theqbz/KicsiKocsi/rajzok/cover.jpg

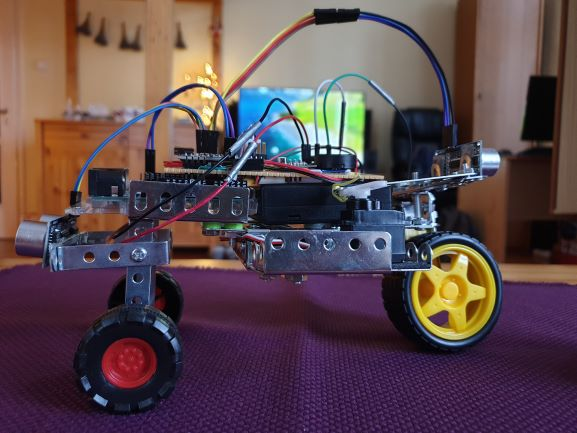
rajzok/cover.jpg
