theqbz/KicsiKocsi/rajzok/kicsikocsi1.jpg

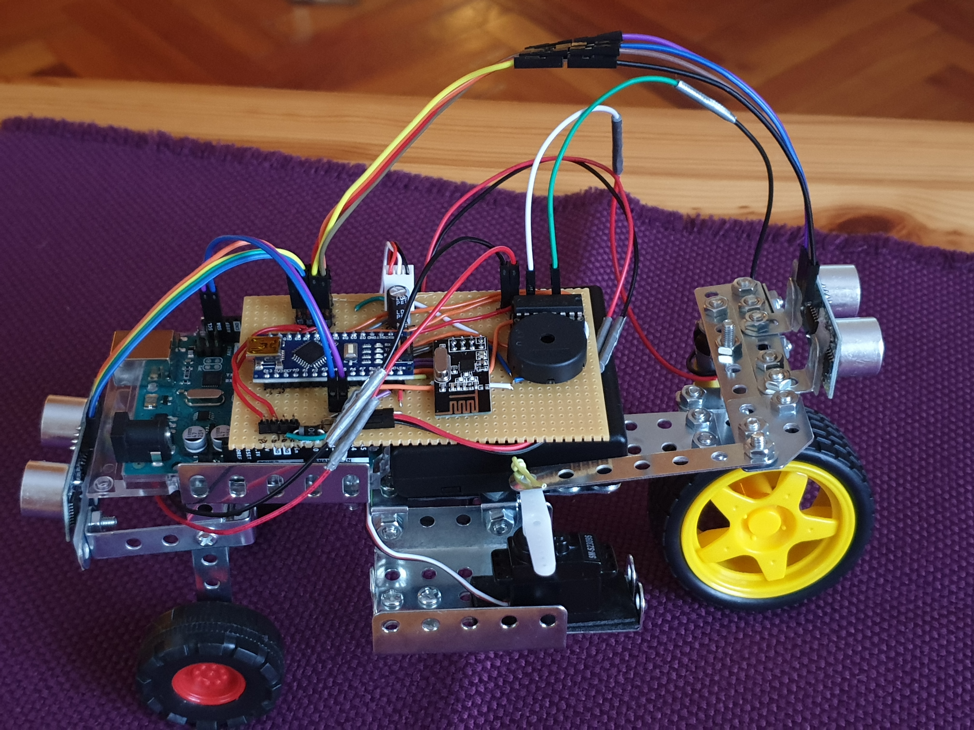
rajzok/kicsikocsi1.jpg
