theqbz/KicsiKocsi/rajzok/kicsikocsi3.jpg

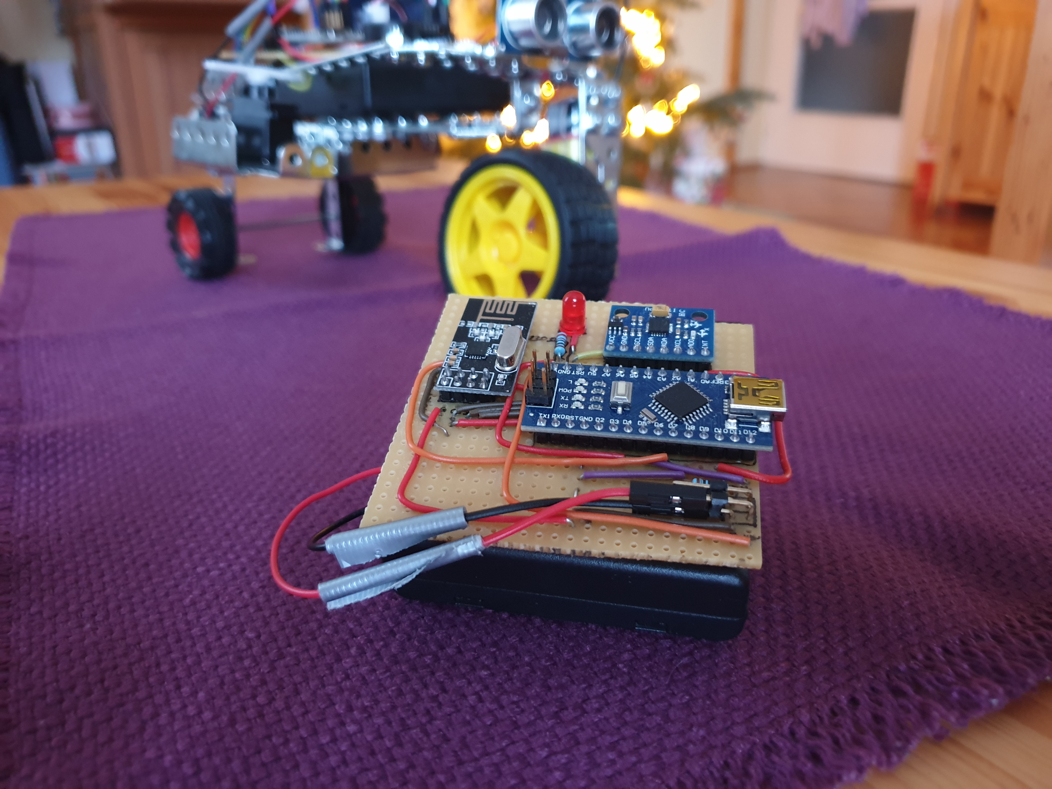
rajzok/kicsikocsi3.jpg
