theqbz/KicsiKocsi/rajzok/kicsikocsi4.jpg

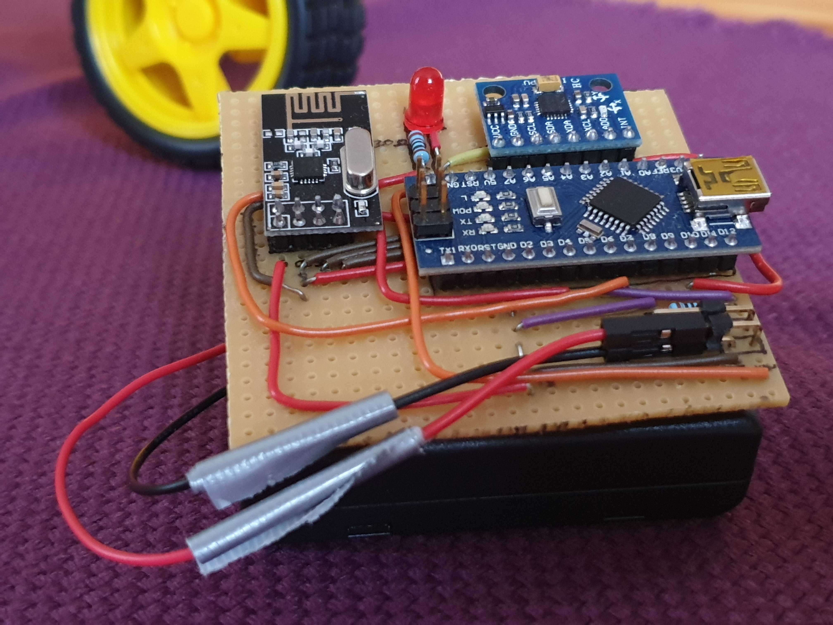
rajzok/kicsikocsi4.jpg
