theqbz/KicsiKocsi/rajzok/központ_bb.jpg

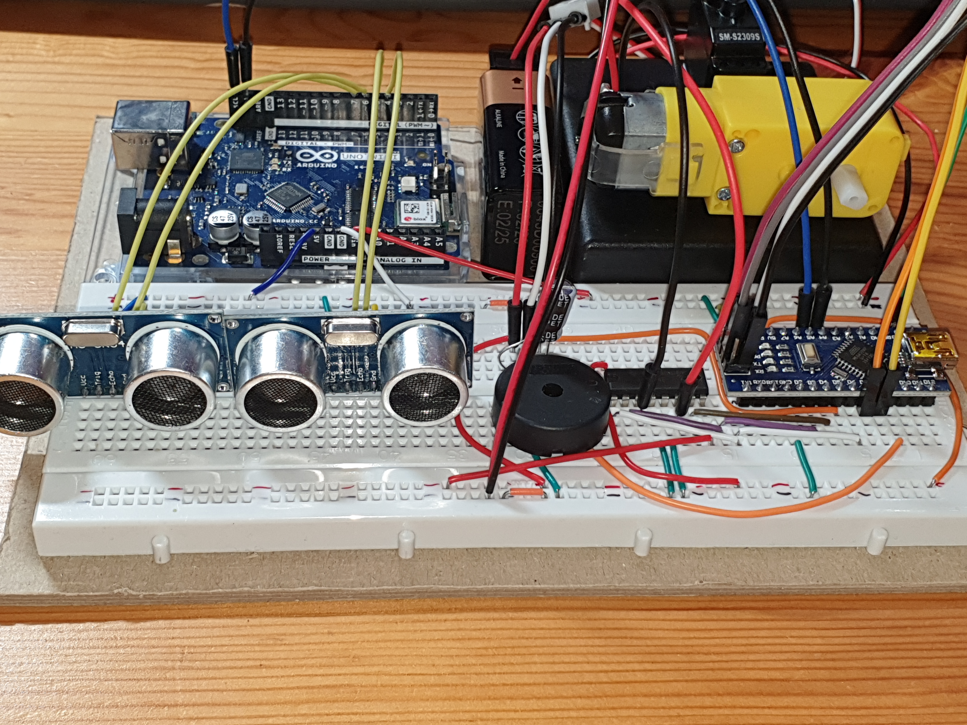
rajzok/központ_bb.jpg
