theqbz/KicsiKocsi/rajzok/távirányító_bb2.jpg

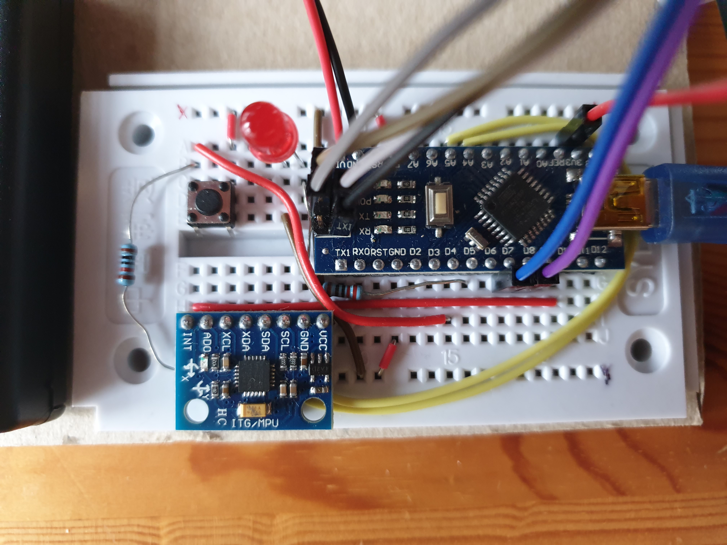
rajzok/távirányító_bb2.jpg
