theqbz/KicsiKocsi/rajzok/Távirányító_breadboard.jpg

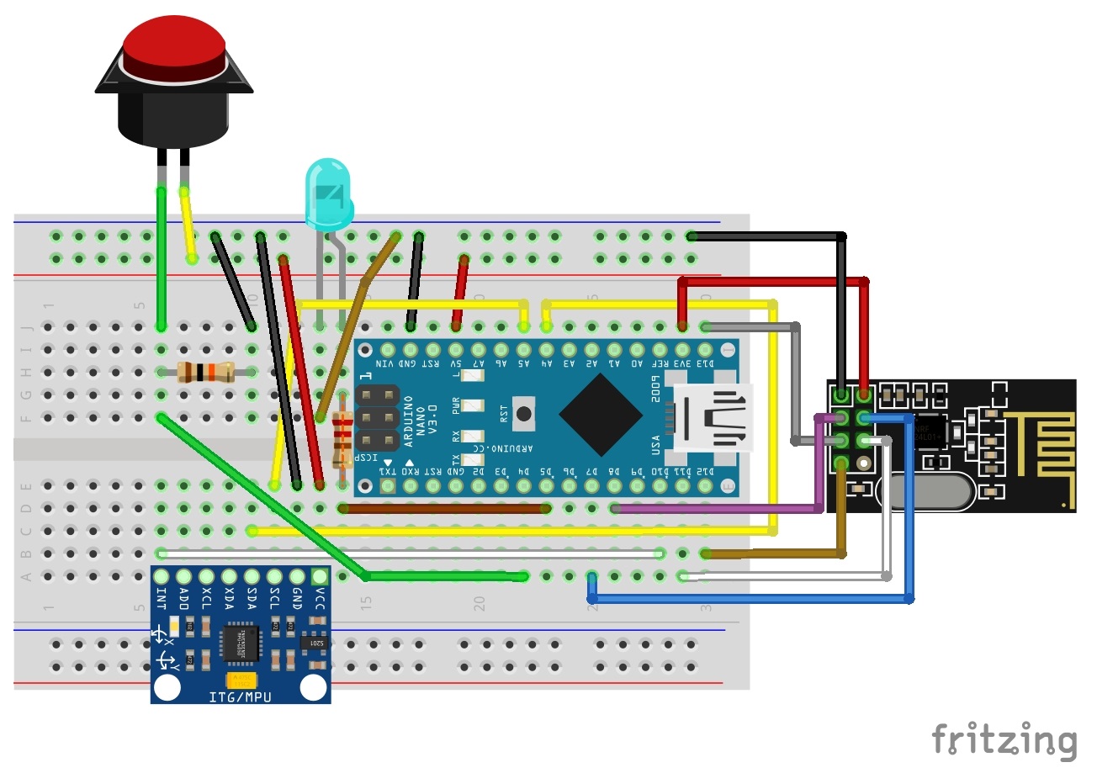
rajzok/Távirányító_breadboard.jpg
