theqbz/KicsiKocsi/rajzok/ÚjKözpont_schem.png

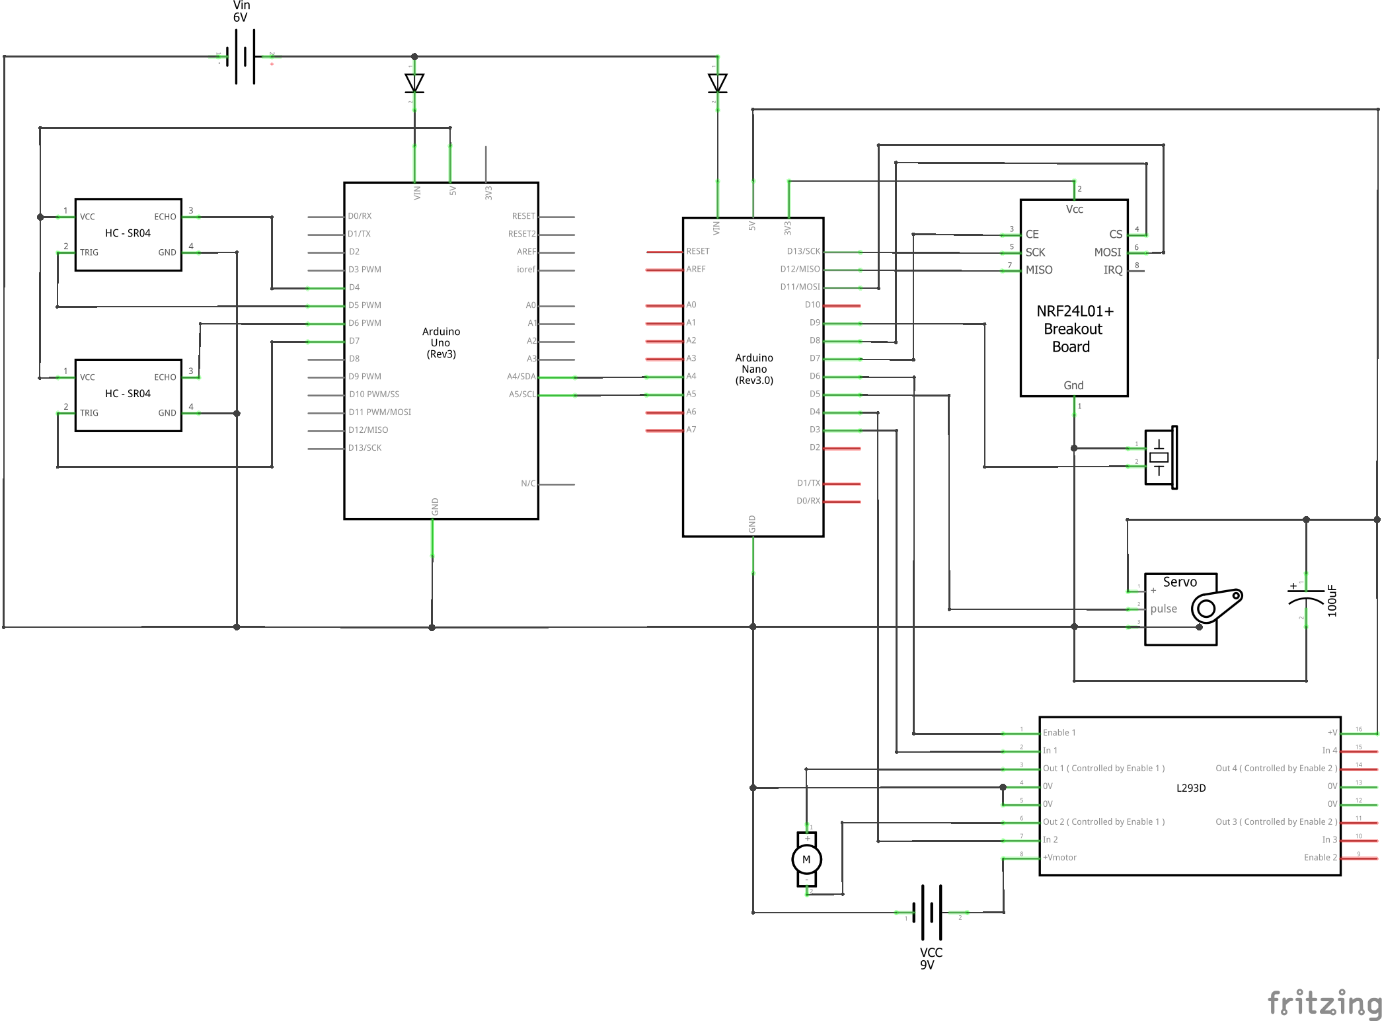
rajzok/ÚjKözpont_schem.png
