theqbz/KicsiKocsi/rajzok/fémépítő.jpg

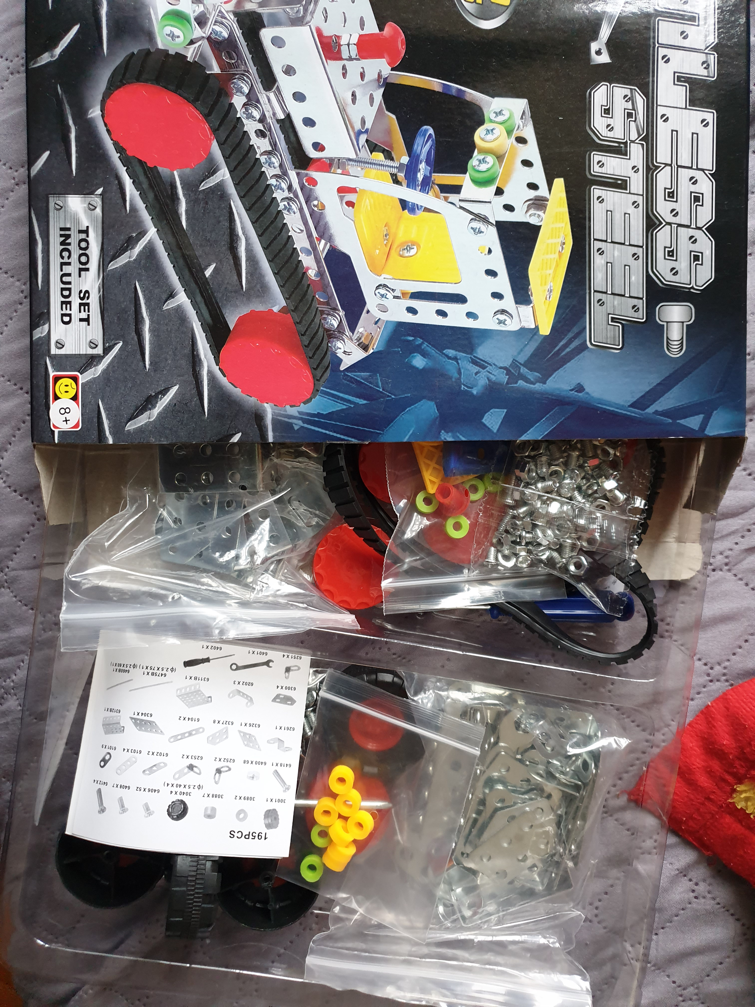
rajzok/fémépítő.jpg
